maynej/EscornaFlex/Imatges/IMG_20191001_191532_987_2.jpg

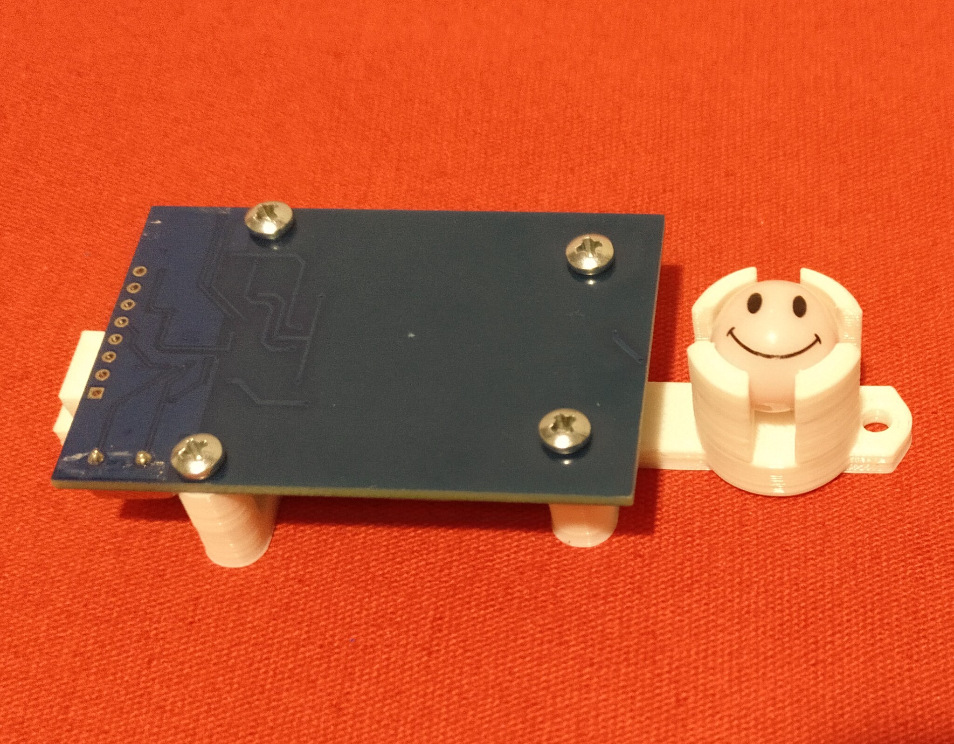
Imatges/IMG_20191001_191532_987_2.jpg
