maynej/EscornaFlex/Imatges/IMG_20191001_230227_612_2.jpg

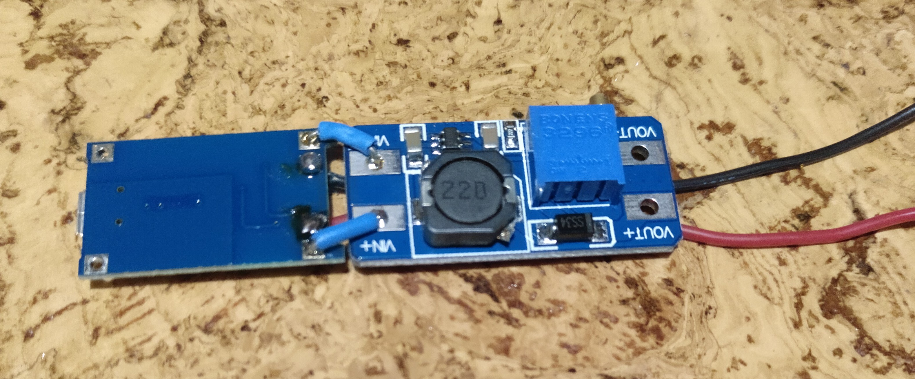
Imatges/IMG_20191001_230227_612_2.jpg
