maynej/EscornaFlex/Imatges/IMG_20191001_231554_312_2.jpg

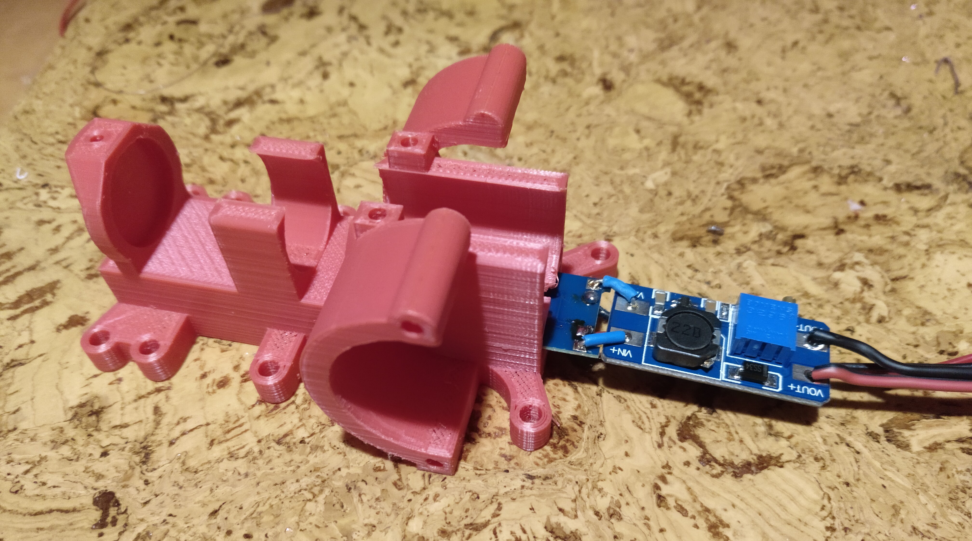
Imatges/IMG_20191001_231554_312_2.jpg
