maynej/EscornaFlex/Imatges/MVIMG_20191001_185445_092_2.jpg

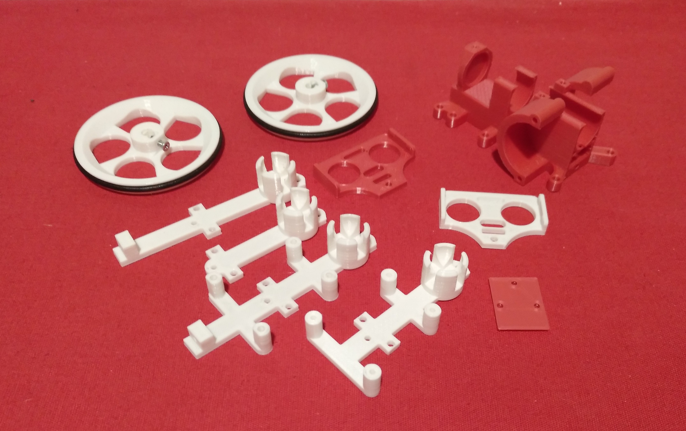
Imatges/MVIMG_20191001_185445_092_2.jpg
